mike-rankin/ESP_trINKet/Images/IMG_0586.JPG

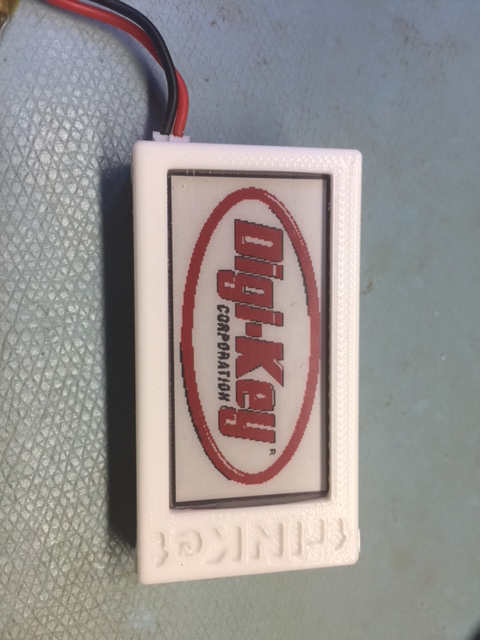
Images/IMG_0586.JPG
