mike-rankin/ESP_trINKet/Images/IMG_0587.JPG

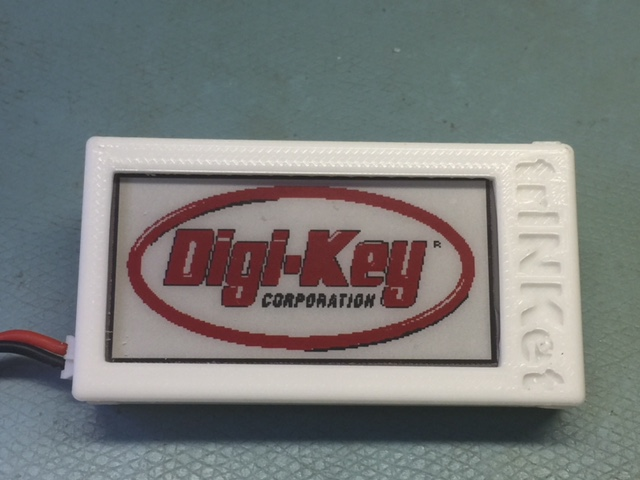
Images/IMG_0587.JPG
