mike-rankin/ESP_trINKet/Images/IMG_0588.JPG

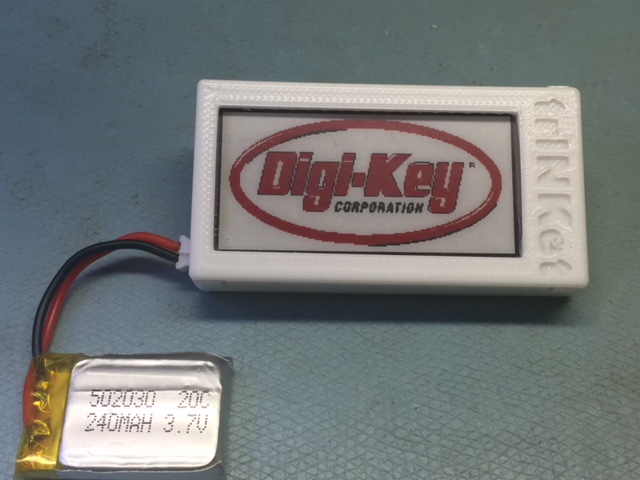
Images/IMG_0588.JPG
